PanosEconomou/open-keyboard/case/gasket-mount-v1/render/iso_green.png

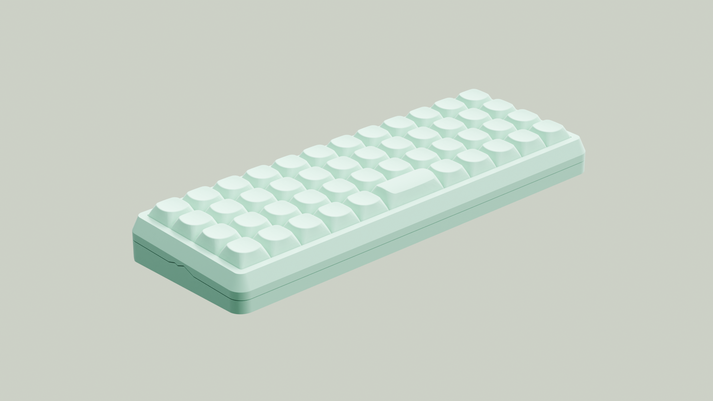
case/gasket-mount-v1/render/iso_green.png
