PanosEconomou/open-keyboard/case/gasket-mount-v1/render/iso_green_base_no_matrix.png

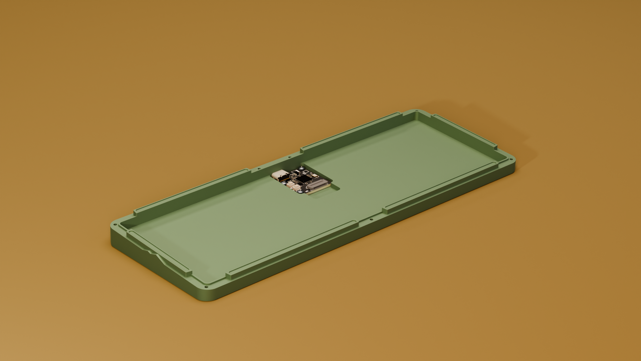
case/gasket-mount-v1/render/iso_green_base_no_matrix.png
