PanosEconomou/open-keyboard/pcb/gasket-mount/matrix/EasyEDA_Step/TF31-18S-0.5SH_800_.step

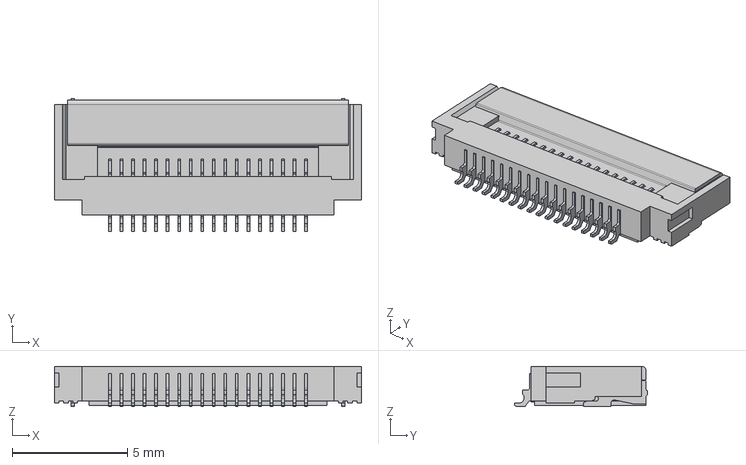
[picture p22: CAD file, 2026-07-09]
pcb/gasket-mount/matrix/EasyEDA_Step/TF31-18S-0.5SH_800_.step
13.3 x 5.75 x 1.75 mm
