PanosEconomou/open-keyboard/case/gasket-mount-v0/exports/gasket-mount-keyboard-bottom-plate.step

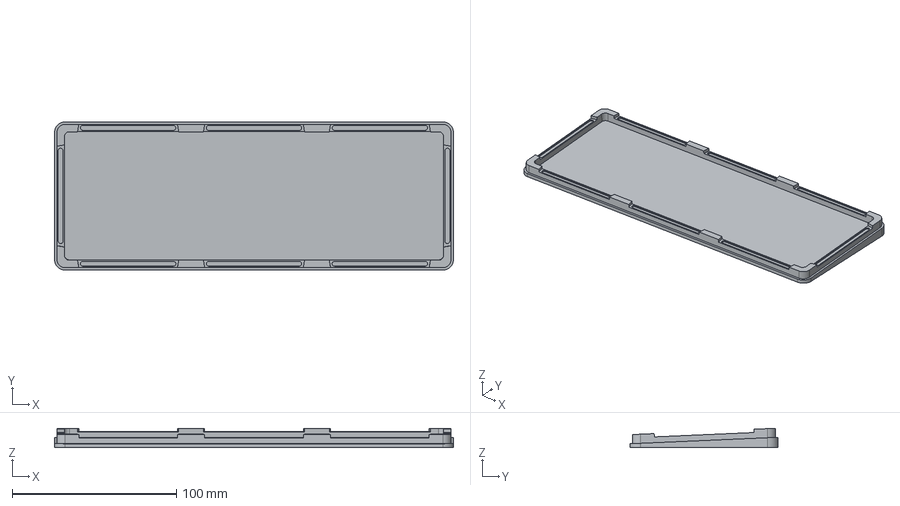
[picture p23: CAD file, 2026-06-08, an earlier design]
case/gasket-mount-v0/exports/gasket-mount-keyboard-bottom-plate.step
242.6 x 90.1 x 11.8 mm
