PanosEconomou/open-keyboard/case/gasket-mount-v0/gasket-mount-keyboard.FCStd

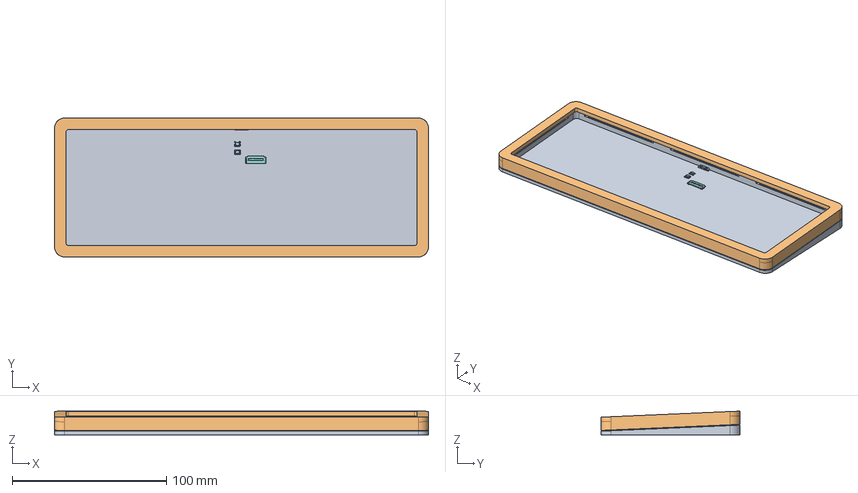
[picture p24: CAD file, 2026-07-12, an earlier design]
case/gasket-mount-v0/gasket-mount-keyboard.FCStd
242.6 x 90.1 x 15.4 mm
bottom-plate
top-plate
C_0402_1005Metric
R_0402_1005Metric
R_0402_1005Metric002
R_0402_1005Metric004
C_0402_1005Metric002
SOT-23-5
C_0402_1005Metric004
C_0402_1005Metric006
C_0402_1005Metric008
C_0402_1005Metric010
Crystal_SMD_Abracon_ABM8G-4Pin_3.2x2.5mm
R_0402_1005Metric006
TF31-18S-0_5SH-198390.PRT
C_0402_1005Metric012
C_0402_1005Metric014
R_0402_1005Metric008
R_0402_1005Metric010
C_0402_1005Metric016
R_0402_1005Metric012
C_0402_1005Metric018
QFN-56-1EP_7x7mm_P0.4mm_EP3.2x3.2mm
C_0402_1005Metric020
C_0402_1005Metric022
SOT-23-6
C_0402_1005Metric024
C_0402_1005Metric026
C_0402_1005Metric028
USB_C_Receptacle_16P_TopMnt_Horizontal_GCT_USB4105-xx-A
C_0402_1005Metric030
C_0402_1005Metric032
R_0402_1005Metric014
controller_copper
controller_pad
controller_via
controller_silkscreen
controller_silkscreen001
controller_soldermask
controller_soldermask001
controller_PCB
