PanosEconomou/open-keyboard/case/gasket-mount-v0/exports/gasket-mount-keyboard-top-plate.step

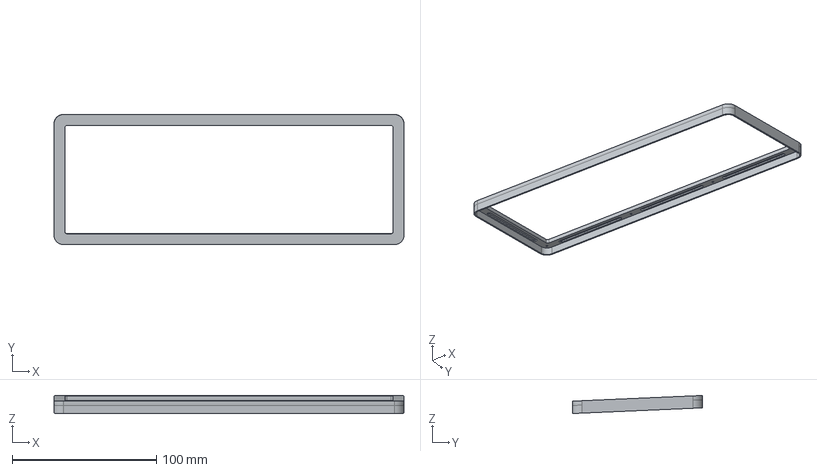
[picture p25: CAD file, 2026-06-08, an earlier design]
case/gasket-mount-v0/exports/gasket-mount-keyboard-top-plate.step
242.6 x 90.2 x 12.5 mm
